menga-team/MES/controller/eagle/controller.sch

## EAGLE design controller/eagle/controller.sch (2022-10-19)

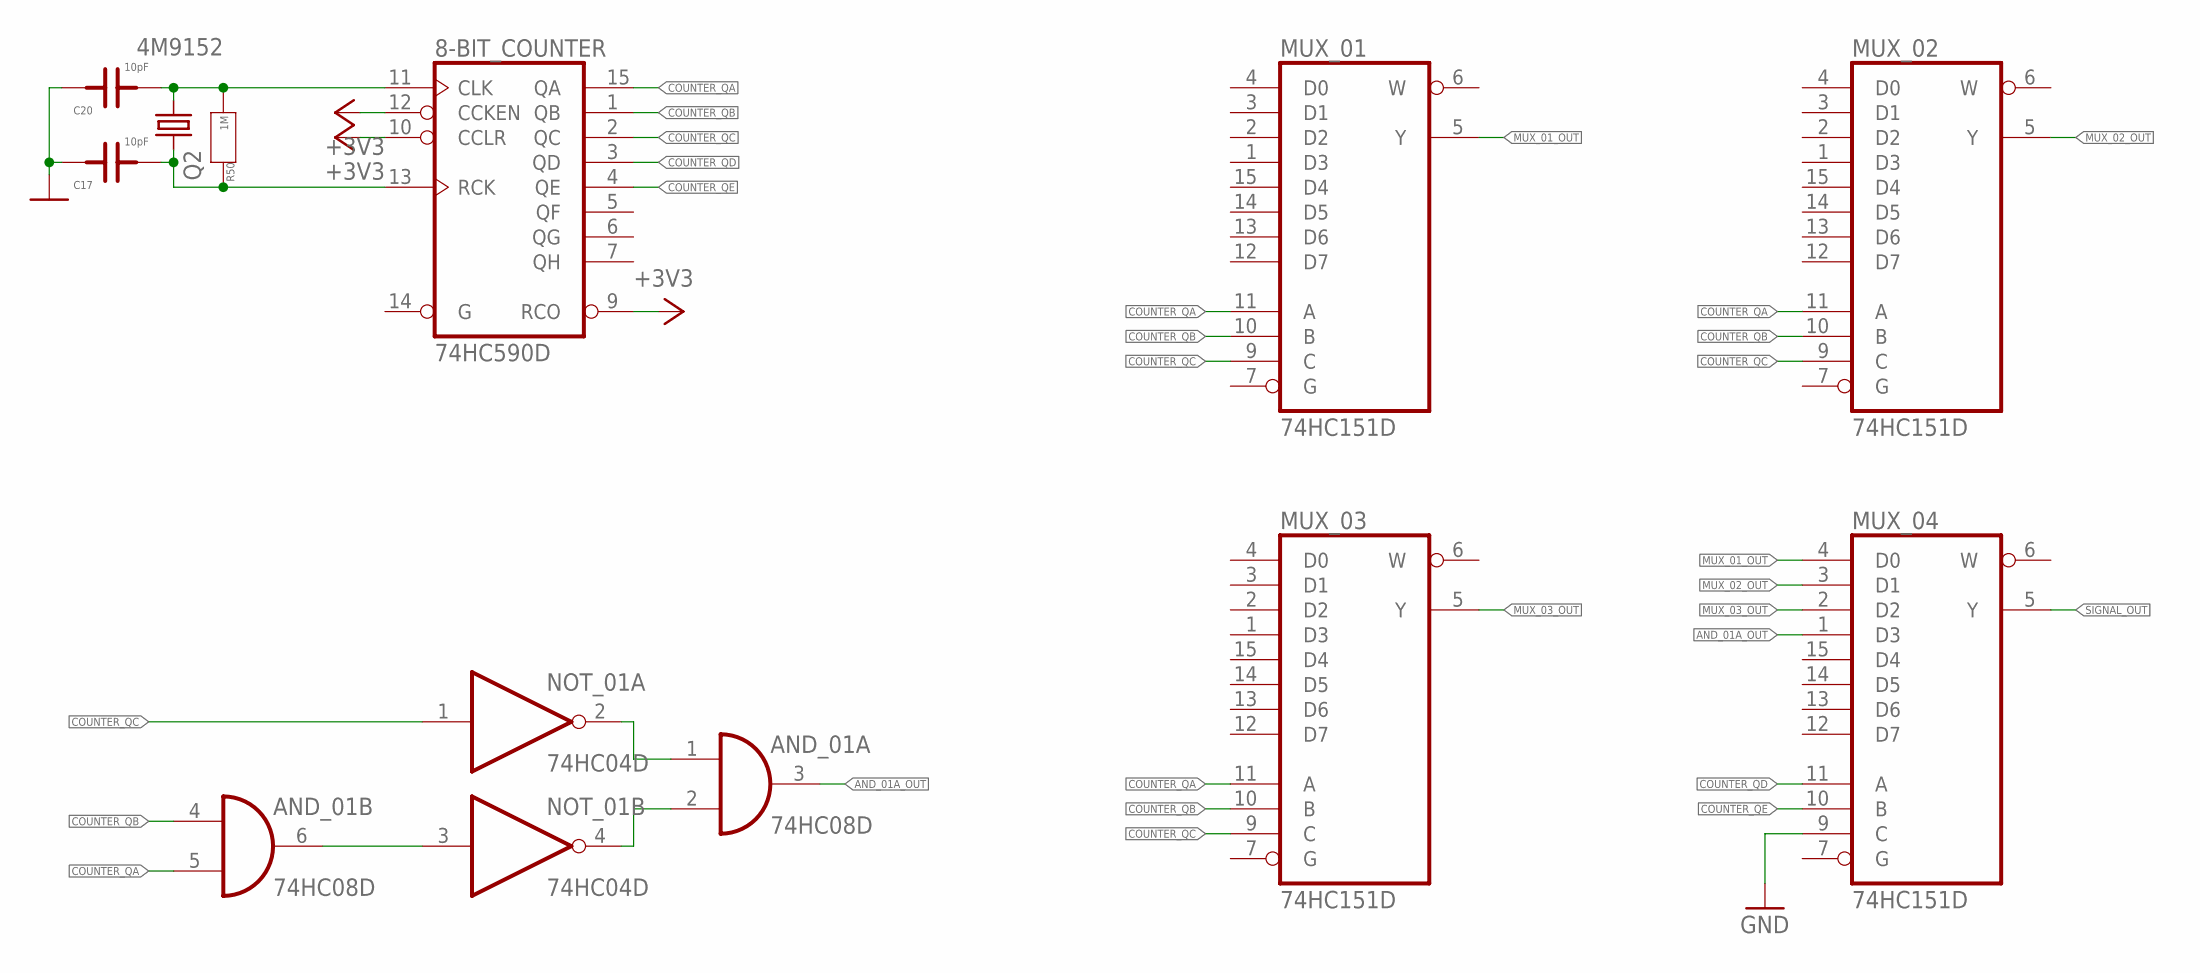
[picture p7: schematic controller.sch, sheet 1]

Parts:
8-BIT_COUNTER: 74HC590D; SO16
AND_01: 74HC08D; SO14
C17, C20: 10pF; 0805F
MUX_01, MUX_02, MUX_03, MUX_04: 74HC151D; SO16
NOT_01: 74HC04D; SO14
Q2: 4M9152; HC49UP
R50: 1M; 0805

Connections:
+3V3: 8-BIT_COUNTER.9 (RCO), 8-BIT_COUNTER.10 (CCLR), 8-BIT_COUNTER.12 (CCKEN)
AND_01A_OUT: AND_01.3 (O), MUX_04.1 (D3)
COUNTER_QA: 8-BIT_COUNTER.15 (QA), AND_01.5 (I1), MUX_01.11 (A), MUX_02.11 (A), MUX_03.11 (A)
COUNTER_QB: 8-BIT_COUNTER.1 (QB), AND_01.4 (I0), MUX_01.10 (B), MUX_02.10 (B), MUX_03.10 (B)
COUNTER_QC: 8-BIT_COUNTER.2 (QC), MUX_01.9 (C), MUX_02.9 (C), MUX_03.9 (C), NOT_01.1 (I)
COUNTER_QD: 8-BIT_COUNTER.3 (QD), MUX_04.11 (A)
COUNTER_QE: 8-BIT_COUNTER.4 (QE), MUX_04.10 (B)
EXTAL: 8-BIT_COUNTER.11 (CLK), C20.1, Q2.1, R50.1
GND: C17.2, C20.2, MUX_04.9 (C)
MUX_01_OUT: MUX_01.5 (Y), MUX_04.4 (D0)
MUX_02_OUT: MUX_02.5 (Y), MUX_04.3 (D1)
MUX_03_OUT: MUX_03.5 (Y), MUX_04.2 (D2)
unnamed: 8-BIT_COUNTER.13 (RCK), C17.1, Q2.2, R50.2
unnamed: AND_01.6 (O), NOT_01.3 (I)
unnamed: AND_01.1 (I0), NOT_01.2 (O)
unnamed: AND_01.2 (I1), NOT_01.4 (O)
SIGNAL_OUT: MUX_04.5 (Y)

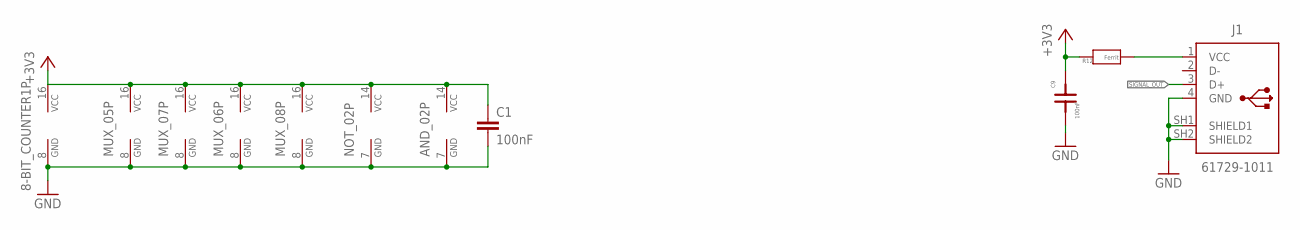
[picture p8: schematic controller.sch, sheet 2]

Parts:
8-BIT_COUNTER1: 74HC590D; SO16
AND_02: 74HC08D; SO14
C1: 100nF; C0805
C9: 100nF; 0805F
J1: 61729-1011; 61729-1011BLF
MUX_05, MUX_06, MUX_07, MUX_08: 74HC151D; SO16
NOT_02: 74HC04D; SO14
R12: Ferrit; 1206

Connections:
+3.3V: 8-BIT_COUNTER1.16 (VCC), AND_02.14 (VCC), C1.1, MUX_05.16 (VCC), MUX_06.16 (VCC), MUX_07.16 (VCC), MUX_08.16 (VCC), NOT_02.14 (VCC)
+3V3: C9.2, R12.2
GND: 8-BIT_COUNTER1.8 (GND), AND_02.7 (GND), C1.2, C9.1, MUX_05.8 (GND), MUX_06.8 (GND), MUX_07.8 (GND), MUX_08.8 (GND), NOT_02.7 (GND)
unnamed: J1.1 (VCC), R12.1
SHIELD1: J1.4 (GND), J1.SH1 (SHIELD1), J1.SH2 (SHIELD2)
SIGNAL_OUT: J1.3 (D+)
