menga-team/MES/cpu/mescpu/create_dummy_game.py

#!/usr/bin/env python3

import os
import sys

bin_file = sys.argv[1]

with open(bin_file, "rb") as asset:
    print("#include <stdint.h>\n");
    print('const uint8_t __attribute__((section(".game-bin"))) hello_world[] = {');
    print("\t", end="")
    while (byte := asset.read(1)):
        print(f"0x{byte.hex()}, ", end="")
    print("\n};\n")
